ComNets-Bremen/GeoSensor/Thesis/Source/src/database.pdf

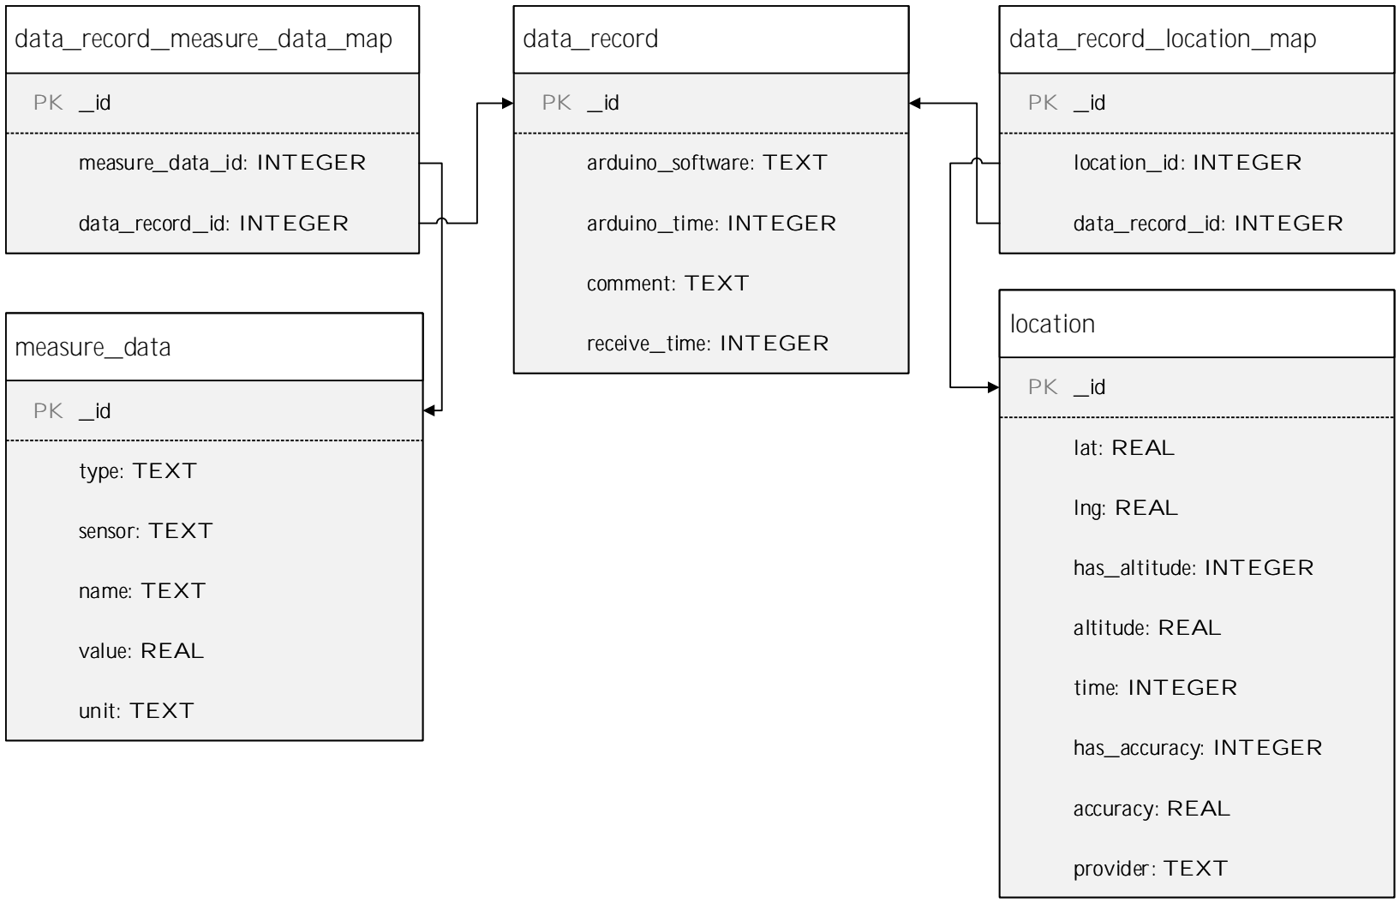
[picture p17: figure]
data_record; arduino_software: TEXT; arduino_time: INTEGER; measure_data; type: TEXT; sensor: TEXT; location; lat: REAL; lng: REAL; receive_time: INTEGER; comment: TEXT; has_altitude: INTEGER; altitude: REAL; time: INTEGER; has_accuracy: INTEGER; accuracy: REAL; provider: TEXT; unit: TEXT; value: REAL; name: TEXT; data_record_location_map; location_id: INTEGER; data_record_id: INTEGER; data_record_measure_data_map; measure_data_id: INTEGER
