ComNets-Bremen/GeoSensor/Thesis/Source/symbols.tex

\label{Symbols}

\stepcounter{chapter}

\setlength{\LTpre}{0pt}
\setlength{\LTpost}{0pt}
{\small
  \begin{longtable}[c]{cp{0.16\textwidth}cp{0.55\textwidth}}
    \caption{List of used mathematical symbols\label{Tab:Symbols}}\\[-2mm]
    \toprule
     & & \sbf{See} & \\
    \rb{\sbf{Symbol}} & \multicolumn{1}{c}{\rb{\sbf{Area}}} &
    \sbf{Page} & \multicolumn{1}{c}{\rb{\sbf{Meaning}}} \\
    \midrule\addlinespace
    \endfirsthead
    \caption[]{List of used mathematical symbols (continued)}\\[-2mm]
    \toprule
     & & \sbf{See} & \\
    \rb{\sbf{Symbol}} & \multicolumn{1}{c}{\rb{\sbf{Area}}} &
    \sbf{Page} & \multicolumn{1}{c}{\rb{\sbf{Meaning}}} \\
    \midrule\addlinespace
    \endhead
    \bottomrule
    \endfoot

    % $a$ & Kanalcodierung &
    % \pageref{Fz:Bitverwuerfelung}
    % & Distanz der Bitverw�rferlung\\
    %
    % $B(m)$ & $\pi/4$--DQPSK & \pageref{Fz:Modulationsbitfolge}
    % & Modulationsbitfolge \\
    %
    % $B_i(m)$ & Kanalcodierung &
    % \pageref{Fz:Bloecke_der_Kanalcodierungsstufe_i}
    % & Bl�cke der Kanalcodierungsstufe $i = 1, 2, \ldots\!, 5$\\
    %
    % $b_i(k)$ & Kanalcodierung &
    % \pageref{Fz:Bits_der_Kanalcodierungsstufe_i}
    % & Bits der Kanalcodierungsstufe $i = 1, 2, \ldots\!, 5$\\
    %
    % $c(X)$ & Kanalcodierung &
    % \pageref{Fz:Generator_Verschluesselungssequenz}
    % & Generatorpolynom der Verschl�sselungssequenz der vierten
    % Kanalcodierungsstufe \\
    %
    % $s(t)$ & $\pi/4$--DQPSK & \pageref{Fz:Komplexe_Einhuellende}
    % & Komplexe Einh�llende des modulierten Signals $M(t)$\\

  \end{longtable}}
