ComNets-Bremen/GeoSensor/Thesis/Source/src/excel_heatmap.PNG

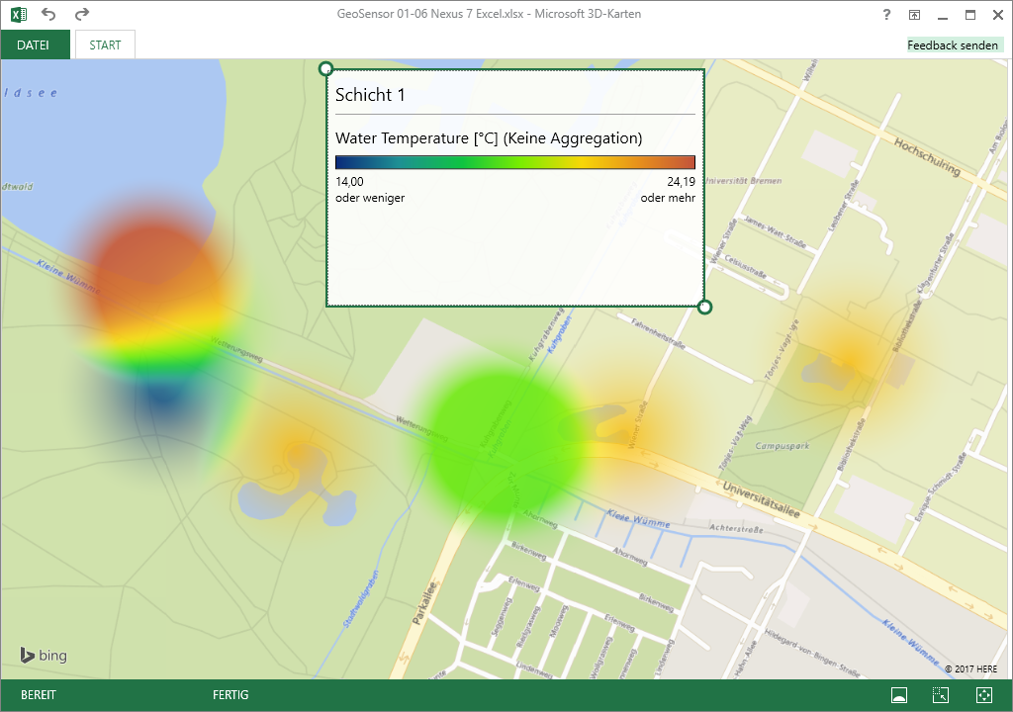
Thesis/Source/src/excel_heatmap.PNG
