ComNets-Bremen/GeoSensor/Thesis/Source/src/settings_en_2.png

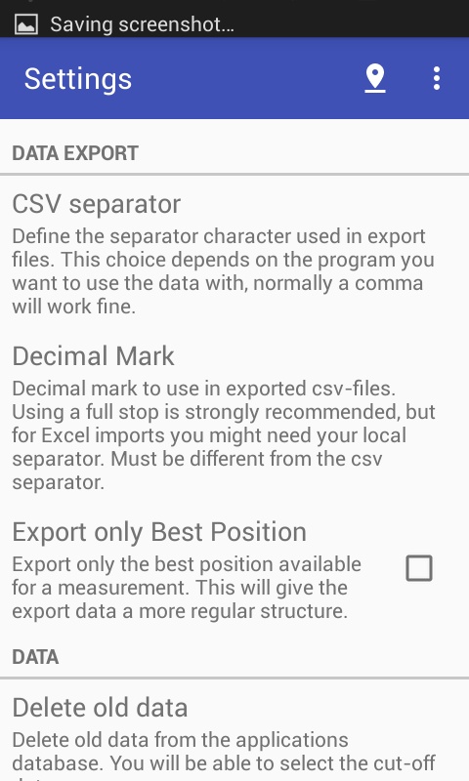
Thesis/Source/src/settings_en_2.png
