ComNets-Bremen/GeoSensor/Thesis/Source/src/settings_en_3.png

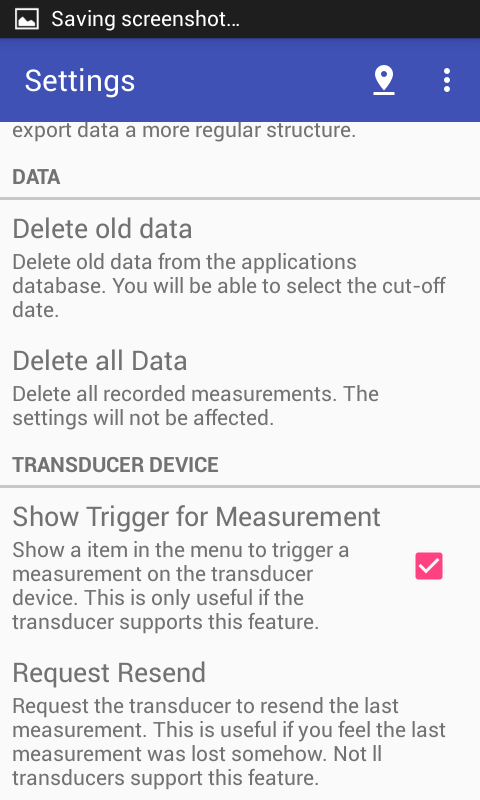
Thesis/Source/src/settings_en_3.png
