ComNets-Bremen/GeoSensor/Other/Materials for Google Play/Screenshots English/Screenshot_20170720-183423.png

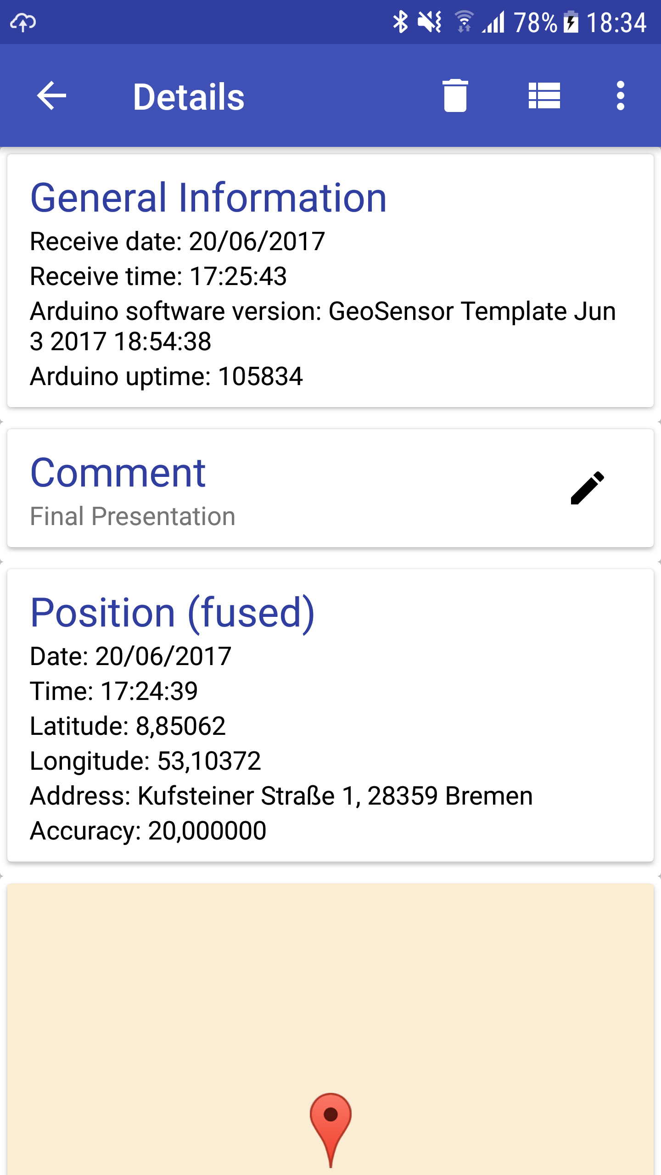
Other/Materials for Google Play/Screenshots English/Screenshot_20170720-183423.png
