ComNets-Bremen/GeoSensor/Other/Materials for Google Play/Screenshots German/Screenshot_20170720-182829.png

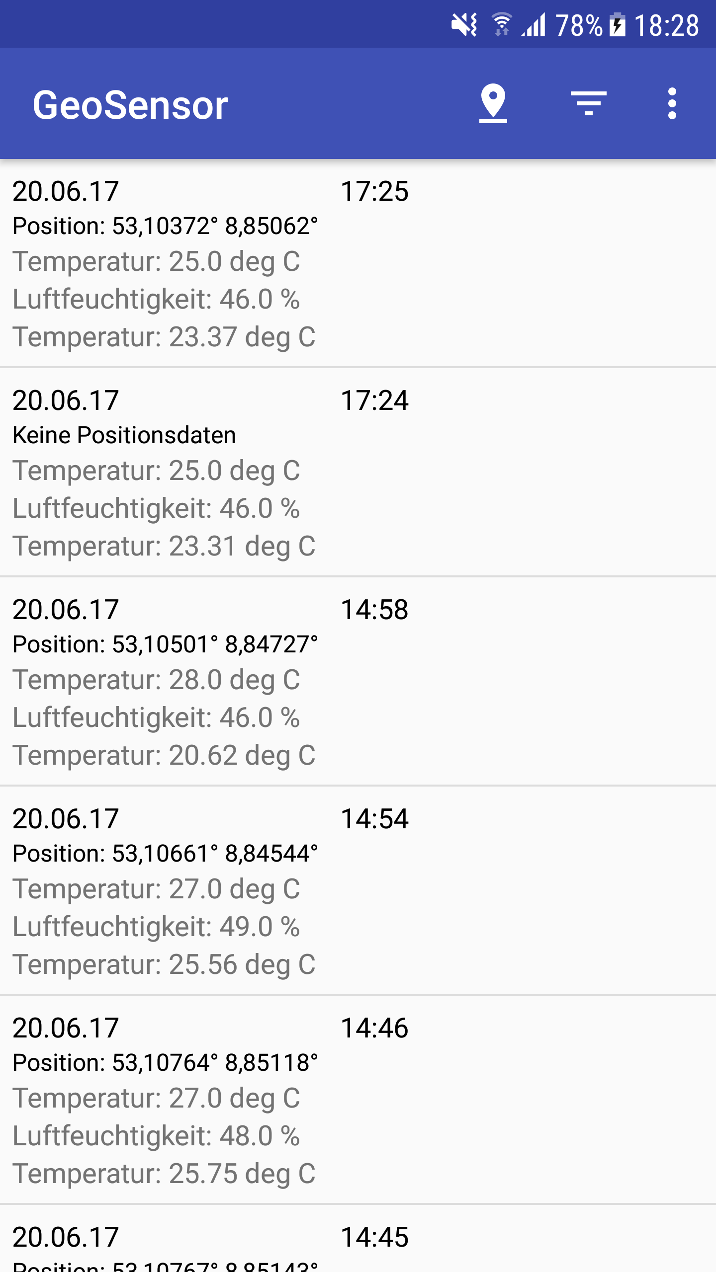
Other/Materials for Google Play/Screenshots German/Screenshot_20170720-182829.png
