ComNets-Bremen/GeoSensor/Other/Materials for Google Play/Screenshots German/Screenshot_20170720-183224.png

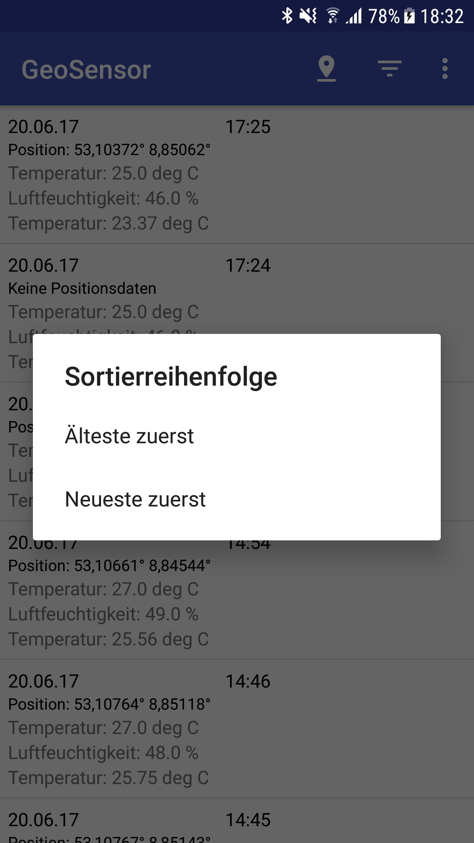
Other/Materials for Google Play/Screenshots German/Screenshot_20170720-183224.png
