ComNets-Bremen/GeoSensor/Tests/energy/system_bluetooth_bare_clean.csv

19:51:05 | 03.30V | 0.000A | 03.30V | 0.000A | OP0 --- --- RM1
19:51:06 | 03.30V | 0.000A | 03.30V | 0.000A | OP0 --- --- RM1
19:51:07 | 03.30V | 0.000A | 03.30V | 0.000A | OP0 --- --- RM1
19:51:08 | 02.47V | 0.004A | 03.28V | 0.027A | OP1 CV1 CV2 RM1
19:51:09 | 03.28V | 0.037A | 03.28V | 0.025A | OP1 CV1 CV2 RM1
19:51:10 | 03.28V | 0.036A | 03.28V | 0.035A | OP1 CV1 CV2 RM1
19:51:11 | 03.28V | 0.037A | 03.28V | 0.017A | OP1 CV1 CV2 RM1
19:51:13 | 03.28V | 0.035A | 03.28V | 0.019A | OP1 CV1 CV2 RM1
19:51:14 | 03.28V | 0.035A | 03.28V | 0.019A | OP1 CV1 CV2 RM1
19:51:15 | 03.28V | 0.034A | 03.28V | 0.018A | OP1 CV1 CV2 RM1
19:51:16 | 03.28V | 0.035A | 03.28V | 0.019A | OP1 CV1 CV2 RM1
19:51:17 | 03.28V | 0.034A | 03.28V | 0.002A | OP1 CV1 CV2 RM1
19:51:18 | 03.28V | 0.035A | 03.28V | 0.004A | OP1 CV1 CV2 RM1
19:51:19 | 03.28V | 0.034A | 03.28V | 0.002A | OP1 CV1 CV2 RM1
19:51:20 | 03.28V | 0.036A | 03.28V | 0.002A | OP1 CV1 CV2 RM1
19:51:21 | 03.28V | 0.034A | 03.28V | 0.002A | OP1 CV1 CV2 RM1
19:51:22 | 03.28V | 0.037A | 03.28V | 0.002A | OP1 CV1 CV2 RM1
19:51:23 | 03.28V | 0.036A | 03.28V | 0.002A | OP1 CV1 CV2 RM1
19:51:24 | 03.28V | 0.037A | 03.28V | 0.003A | OP1 CV1 CV2 RM1
19:51:25 | 03.28V | 0.036A | 03.28V | 0.003A | OP1 CV1 CV2 RM1
19:51:26 | 03.28V | 0.037A | 03.28V | 0.004A | OP1 CV1 CV2 RM1
19:51:27 | 03.28V | 0.036A | 03.28V | 0.002A | OP1 CV1 CV2 RM1
19:51:28 | 03.28V | 0.037A | 03.28V | 0.002A | OP1 CV1 CV2 RM1
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
19:58:39 | 03.28V | 0.005A | 03.28V | 0.002A | OP1 CV1 CV2 RM1
19:58:40 | 03.28V | 0.005A | 03.28V | 0.002A | OP1 CV1 CV2 RM1
19:58:41 | 03.28V | 0.005A | 03.28V | 0.005A | OP1 CV1 CV2 RM1
19:58:42 | 03.28V | 0.005A | 03.28V | 0.002A | OP1 CV1 CV2 RM1
