ComNets-Bremen/GeoSensor/Thesis/Source/src/field_test_excel_windows.PNG

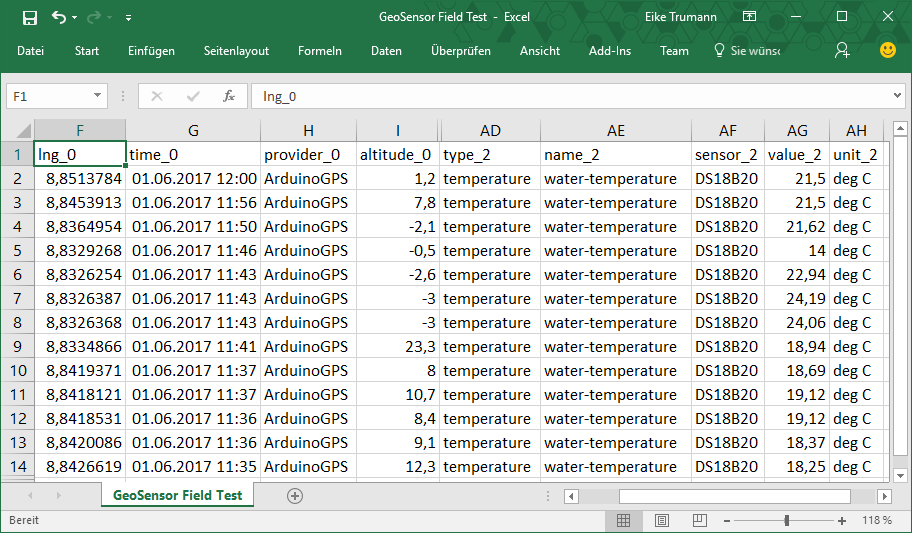
Thesis/Source/src/field_test_excel_windows.PNG
