ComNets-Bremen/GeoSensor/Arduino Documentation/Demonstration Device Circuit.pdf

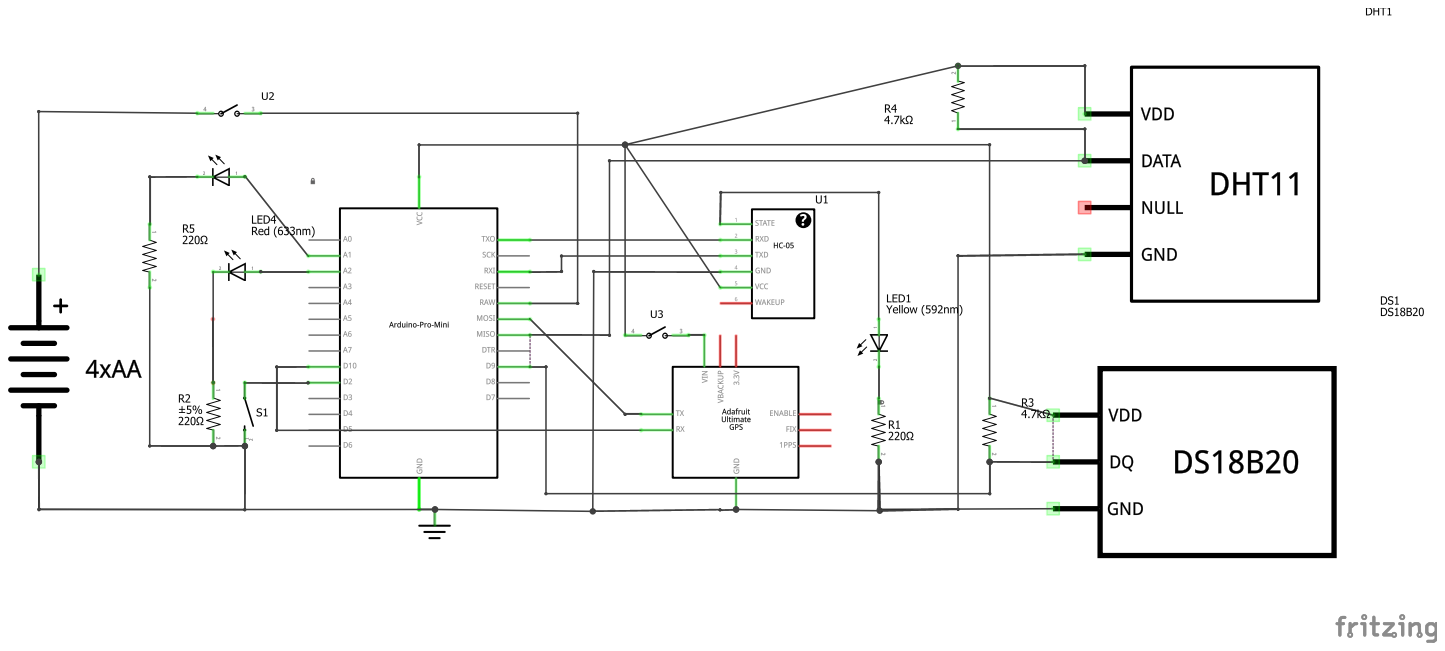
[picture p48: page 1]
